RavuAlHemio/trainbuttons/code/on_board/stm32g0b0/src/adc/cr.rs

#[doc = "Register `CR` reader"]
pub type R = crate::R<CrSpec>;
#[doc = "Register `CR` writer"]
pub type W = crate::W<CrSpec>;
#[doc = "ADC enable command This bit is set by software to enable the ADC. The ADC is effectively ready to operate once the ADRDY flag has been set. It is cleared by hardware when the ADC is disabled, after the execution of the ADDIS command. Note: The software is allowed to set ADEN only when all bits of ADC_CR registers are 0 (ADCAL=0, ADSTP=0, ADSTART=0, ADDIS=0 and ADEN=0)\n\nValue on reset: 0"]
#[derive(Clone, Copy, Debug, PartialEq, Eq)]
pub enum Aden {
    #[doc = "0: ADC is disabled (OFF state)"]
    B0x0 = 0,
    #[doc = "1: Write 1 to enable the ADC."]
    B0x1 = 1,
}
impl From<Aden> for bool {
    #[inline(always)]
    fn from(variant: Aden) -> Self {
        variant as u8 != 0
    }
}
#[doc = "Field `ADEN` reader - ADC enable command This bit is set by software to enable the ADC. The ADC is effectively ready to operate once the ADRDY flag has been set. It is cleared by hardware when the ADC is disabled, after the execution of the ADDIS command. Note: The software is allowed to set ADEN only when all bits of ADC_CR registers are 0 (ADCAL=0, ADSTP=0, ADSTART=0, ADDIS=0 and ADEN=0)"]
pub type AdenR = crate::BitReader<Aden>;
impl AdenR {
    #[doc = "Get enumerated values variant"]
    #[inline(always)]
    pub const fn variant(&self) -> Aden {
        match self.bits {
            false => Aden::B0x0,
            true => Aden::B0x1,
        }
    }
    #[doc = "ADC is disabled (OFF state)"]
    #[inline(always)]
    pub fn is_b_0x0(&self) -> bool {
        *self == Aden::B0x0
    }
    #[doc = "Write 1 to enable the ADC."]
    #[inline(always)]
    pub fn is_b_0x1(&self) -> bool {
        *self == Aden::B0x1
    }
}
#[doc = "Field `ADEN` writer - ADC enable command This bit is set by software to enable the ADC. The ADC is effectively ready to operate once the ADRDY flag has been set. It is cleared by hardware when the ADC is disabled, after the execution of the ADDIS command. Note: The software is allowed to set ADEN only when all bits of ADC_CR registers are 0 (ADCAL=0, ADSTP=0, ADSTART=0, ADDIS=0 and ADEN=0)"]
pub type AdenW<'a, REG> = crate::BitWriter<'a, REG, Aden>;
impl<'a, REG> AdenW<'a, REG>
where
    REG: crate::Writable + crate::RegisterSpec,
{
    #[doc = "ADC is disabled (OFF state)"]
    #[inline(always)]
    pub fn b_0x0(self) -> &'a mut crate::W<REG> {
        self.variant(Aden::B0x0)
    }
    #[doc = "Write 1 to enable the ADC."]
    #[inline(always)]
    pub fn b_0x1(self) -> &'a mut crate::W<REG> {
        self.variant(Aden::B0x1)
    }
}
#[doc = "ADC disable command This bit is set by software to disable the ADC (ADDIS command) and put it into power-down state (OFF state). It is cleared by hardware once the ADC is effectively disabled (ADEN is also cleared by hardware at this time). Note: Setting ADDIS to '1' is only effective when ADEN=1 and ADSTART=0 (which ensures that no conversion is ongoing)\n\nValue on reset: 0"]
#[derive(Clone, Copy, Debug, PartialEq, Eq)]
pub enum Addis {
    #[doc = "0: No ADDIS command ongoing"]
    B0x0 = 0,
    #[doc = "1: Write 1 to disable the ADC. Read 1 means that an ADDIS command is in progress."]
    B0x1 = 1,
}
impl From<Addis> for bool {
    #[inline(always)]
    fn from(variant: Addis) -> Self {
        variant as u8 != 0
    }
}
#[doc = "Field `ADDIS` reader - ADC disable command This bit is set by software to disable the ADC (ADDIS command) and put it into power-down state (OFF state). It is cleared by hardware once the ADC is effectively disabled (ADEN is also cleared by hardware at this time). Note: Setting ADDIS to '1' is only effective when ADEN=1 and ADSTART=0 (which ensures that no conversion is ongoing)"]
pub type AddisR = crate::BitReader<Addis>;
impl AddisR {
    #[doc = "Get enumerated values variant"]
    #[inline(always)]
    pub const fn variant(&self) -> Addis {
        match self.bits {
            false => Addis::B0x0,
            true => Addis::B0x1,
        }
    }
    #[doc = "No ADDIS command ongoing"]
    #[inline(always)]
    pub fn is_b_0x0(&self) -> bool {
        *self == Addis::B0x0
    }
    #[doc = "Write 1 to disable the ADC. Read 1 means that an ADDIS command is in progress."]
    #[inline(always)]
    pub fn is_b_0x1(&self) -> bool {
        *self == Addis::B0x1
    }
}
#[doc = "Field `ADDIS` writer - ADC disable command This bit is set by software to disable the ADC (ADDIS command) and put it into power-down state (OFF state). It is cleared by hardware once the ADC is effectively disabled (ADEN is also cleared by hardware at this time). Note: Setting ADDIS to '1' is only effective when ADEN=1 and ADSTART=0 (which ensures that no conversion is ongoing)"]
pub type AddisW<'a, REG> = crate::BitWriter<'a, REG, Addis>;
impl<'a, REG> AddisW<'a, REG>
where
    REG: crate::Writable + crate::RegisterSpec,
{
    #[doc = "No ADDIS command ongoing"]
    #[inline(always)]
    pub fn b_0x0(self) -> &'a mut crate::W<REG> {
        self.variant(Addis::B0x0)
    }
    #[doc = "Write 1 to disable the ADC. Read 1 means that an ADDIS command is in progress."]
    #[inline(always)]
    pub fn b_0x1(self) -> &'a mut crate::W<REG> {
        self.variant(Addis::B0x1)
    }
}
#[doc = "ADC start conversion command This bit is set by software to start ADC conversion. Depending on the EXTEN \\[1:0\\]
configuration bits, a conversion either starts immediately (software trigger configuration) or once a hardware trigger event occurs (hardware trigger configuration). It is cleared by hardware: In single conversion mode (CONT=0, DISCEN=0), when software trigger is selected (EXTEN=00): at the assertion of the end of Conversion Sequence (EOS) flag. In discontinuous conversion mode(CONT=0, DISCEN=1), when the software trigger is selected (EXTEN=00): at the assertion of the end of Conversion (EOC) flag. In all other cases: after the execution of the ADSTP command, at the same time as the ADSTP bit is cleared by hardware. Note: The software is allowed to set ADSTART only when ADEN=1 and ADDIS=0 (ADC is enabled and there is no pending request to disable the ADC). After writing to ADC_CHSELR register or changing CHSELRMOD or SCANDIRW, it is mandatory to wait until CCRDY flag is asserted before setting ADSTART, otherwise, the value written to ADSTART is ignored.\n\nValue on reset: 0"]
#[derive(Clone, Copy, Debug, PartialEq, Eq)]
pub enum Adstart {
    #[doc = "0: No ADC conversion is ongoing."]
    B0x0 = 0,
    #[doc = "1: Write 1 to start the ADC. Read 1 means that the ADC is operating and may be converting."]
    B0x1 = 1,
}
impl From<Adstart> for bool {
    #[inline(always)]
    fn from(variant: Adstart) -> Self {
        variant as u8 != 0
    }
}
#[doc = "Field `ADSTART` reader - ADC start conversion command This bit is set by software to start ADC conversion. Depending on the EXTEN \\[1:0\\]
configuration bits, a conversion either starts immediately (software trigger configuration) or once a hardware trigger event occurs (hardware trigger configuration). It is cleared by hardware: In single conversion mode (CONT=0, DISCEN=0), when software trigger is selected (EXTEN=00): at the assertion of the end of Conversion Sequence (EOS) flag. In discontinuous conversion mode(CONT=0, DISCEN=1), when the software trigger is selected (EXTEN=00): at the assertion of the end of Conversion (EOC) flag. In all other cases: after the execution of the ADSTP command, at the same time as the ADSTP bit is cleared by hardware. Note: The software is allowed to set ADSTART only when ADEN=1 and ADDIS=0 (ADC is enabled and there is no pending request to disable the ADC). After writing to ADC_CHSELR register or changing CHSELRMOD or SCANDIRW, it is mandatory to wait until CCRDY flag is asserted before setting ADSTART, otherwise, the value written to ADSTART is ignored."]
pub type AdstartR = crate::BitReader<Adstart>;
impl AdstartR {
    #[doc = "Get enumerated values variant"]
    #[inline(always)]
    pub const fn variant(&self) -> Adstart {
        match self.bits {
            false => Adstart::B0x0,
            true => Adstart::B0x1,
        }
    }
    #[doc = "No ADC conversion is ongoing."]
    #[inline(always)]
    pub fn is_b_0x0(&self) -> bool {
        *self == Adstart::B0x0
    }
    #[doc = "Write 1 to start the ADC. Read 1 means that the ADC is operating and may be converting."]
    #[inline(always)]
    pub fn is_b_0x1(&self) -> bool {
        *self == Adstart::B0x1
    }
}
#[doc = "Field `ADSTART` writer - ADC start conversion command This bit is set by software to start ADC conversion. Depending on the EXTEN \\[1:0\\]
configuration bits, a conversion either starts immediately (software trigger configuration) or once a hardware trigger event occurs (hardware trigger configuration). It is cleared by hardware: In single conversion mode (CONT=0, DISCEN=0), when software trigger is selected (EXTEN=00): at the assertion of the end of Conversion Sequence (EOS) flag. In discontinuous conversion mode(CONT=0, DISCEN=1), when the software trigger is selected (EXTEN=00): at the assertion of the end of Conversion (EOC) flag. In all other cases: after the execution of the ADSTP command, at the same time as the ADSTP bit is cleared by hardware. Note: The software is allowed to set ADSTART only when ADEN=1 and ADDIS=0 (ADC is enabled and there is no pending request to disable the ADC). After writing to ADC_CHSELR register or changing CHSELRMOD or SCANDIRW, it is mandatory to wait until CCRDY flag is asserted before setting ADSTART, otherwise, the value written to ADSTART is ignored."]
pub type AdstartW<'a, REG> = crate::BitWriter<'a, REG, Adstart>;
impl<'a, REG> AdstartW<'a, REG>
where
    REG: crate::Writable + crate::RegisterSpec,
{
    #[doc = "No ADC conversion is ongoing."]
    #[inline(always)]
    pub fn b_0x0(self) -> &'a mut crate::W<REG> {
        self.variant(Adstart::B0x0)
    }
    #[doc = "Write 1 to start the ADC. Read 1 means that the ADC is operating and may be converting."]
    #[inline(always)]
    pub fn b_0x1(self) -> &'a mut crate::W<REG> {
        self.variant(Adstart::B0x1)
    }
}
#[doc = "ADC stop conversion command This bit is set by software to stop and discard an ongoing conversion (ADSTP Command). It is cleared by hardware when the conversion is effectively discarded and the ADC is ready to accept a new start conversion command. Note: Setting ADSTP to '1' is only effective when ADSTART=1 and ADDIS=0 (ADC is enabled and may be converting and there is no pending request to disable the ADC)\n\nValue on reset: 0"]
#[derive(Clone, Copy, Debug, PartialEq, Eq)]
pub enum Adstp {
    #[doc = "0: No ADC stop conversion command ongoing"]
    B0x0 = 0,
    #[doc = "1: Write 1 to stop the ADC. Read 1 means that an ADSTP command is in progress."]
    B0x1 = 1,
}
impl From<Adstp> for bool {
    #[inline(always)]
    fn from(variant: Adstp) -> Self {
        variant as u8 != 0
    }
}
#[doc = "Field `ADSTP` reader - ADC stop conversion command This bit is set by software to stop and discard an ongoing conversion (ADSTP Command). It is cleared by hardware when the conversion is effectively discarded and the ADC is ready to accept a new start conversion command. Note: Setting ADSTP to '1' is only effective when ADSTART=1 and ADDIS=0 (ADC is enabled and may be converting and there is no pending request to disable the ADC)"]
pub type AdstpR = crate::BitReader<Adstp>;
impl AdstpR {
    #[doc = "Get enumerated values variant"]
    #[inline(always)]
    pub const fn variant(&self) -> Adstp {
        match self.bits {
            false => Adstp::B0x0,
            true => Adstp::B0x1,
        }
    }
    #[doc = "No ADC stop conversion command ongoing"]
    #[inline(always)]
    pub fn is_b_0x0(&self) -> bool {
        *self == Adstp::B0x0
    }
    #[doc = "Write 1 to stop the ADC. Read 1 means that an ADSTP command is in progress."]
    #[inline(always)]
    pub fn is_b_0x1(&self) -> bool {
        *self == Adstp::B0x1
    }
}
#[doc = "Field `ADSTP` writer - ADC stop conversion command This bit is set by software to stop and discard an ongoing conversion (ADSTP Command). It is cleared by hardware when the conversion is effectively discarded and the ADC is ready to accept a new start conversion command. Note: Setting ADSTP to '1' is only effective when ADSTART=1 and ADDIS=0 (ADC is enabled and may be converting and there is no pending request to disable the ADC)"]
pub type AdstpW<'a, REG> = crate::BitWriter<'a, REG, Adstp>;
impl<'a, REG> AdstpW<'a, REG>
where
    REG: crate::Writable + crate::RegisterSpec,
{
    #[doc = "No ADC stop conversion command ongoing"]
    #[inline(always)]
    pub fn b_0x0(self) -> &'a mut crate::W<REG> {
        self.variant(Adstp::B0x0)
    }
    #[doc = "Write 1 to stop the ADC. Read 1 means that an ADSTP command is in progress."]
    #[inline(always)]
    pub fn b_0x1(self) -> &'a mut crate::W<REG> {
        self.variant(Adstp::B0x1)
    }
}
#[doc = "ADC Voltage Regulator Enable This bit is set by software, to enable the ADC internal voltage regulator. The voltage regulator output is available after tADCVREG_SETUP. It is cleared by software to disable the voltage regulator. It can be cleared only if ADEN is et to 0. Note: The software is allowed to program this bit field only when the ADC is disabled (ADCAL=0, ADSTART=0, ADSTP=0, ADDIS=0 and ADEN=0).\n\nValue on reset: 0"]
#[derive(Clone, Copy, Debug, PartialEq, Eq)]
pub enum Advregen {
    #[doc = "0: ADC voltage regulator disabled"]
    B0x0 = 0,
    #[doc = "1: ADC voltage regulator enabled"]
    B0x1 = 1,
}
impl From<Advregen> for bool {
    #[inline(always)]
    fn from(variant: Advregen) -> Self {
        variant as u8 != 0
    }
}
#[doc = "Field `ADVREGEN` reader - ADC Voltage Regulator Enable This bit is set by software, to enable the ADC internal voltage regulator. The voltage regulator output is available after tADCVREG_SETUP. It is cleared by software to disable the voltage regulator. It can be cleared only if ADEN is et to 0. Note: The software is allowed to program this bit field only when the ADC is disabled (ADCAL=0, ADSTART=0, ADSTP=0, ADDIS=0 and ADEN=0)."]
pub type AdvregenR = crate::BitReader<Advregen>;
impl AdvregenR {
    #[doc = "Get enumerated values variant"]
    #[inline(always)]
    pub const fn variant(&self) -> Advregen {
        match self.bits {
            false => Advregen::B0x0,
            true => Advregen::B0x1,
        }
    }
    #[doc = "ADC voltage regulator disabled"]
    #[inline(always)]
    pub fn is_b_0x0(&self) -> bool {
        *self == Advregen::B0x0
    }
    #[doc = "ADC voltage regulator enabled"]
    #[inline(always)]
    pub fn is_b_0x1(&self) -> bool {
        *self == Advregen::B0x1
    }
}
#[doc = "Field `ADVREGEN` writer - ADC Voltage Regulator Enable This bit is set by software, to enable the ADC internal voltage regulator. The voltage regulator output is available after tADCVREG_SETUP. It is cleared by software to disable the voltage regulator. It can be cleared only if ADEN is et to 0. Note: The software is allowed to program this bit field only when the ADC is disabled (ADCAL=0, ADSTART=0, ADSTP=0, ADDIS=0 and ADEN=0)."]
pub type AdvregenW<'a, REG> = crate::BitWriter<'a, REG, Advregen>;
impl<'a, REG> AdvregenW<'a, REG>
where
    REG: crate::Writable + crate::RegisterSpec,
{
    #[doc = "ADC voltage regulator disabled"]
    #[inline(always)]
    pub fn b_0x0(self) -> &'a mut crate::W<REG> {
        self.variant(Advregen::B0x0)
    }
    #[doc = "ADC voltage regulator enabled"]
    #[inline(always)]
    pub fn b_0x1(self) -> &'a mut crate::W<REG> {
        self.variant(Advregen::B0x1)
    }
}
#[doc = "ADC calibration This bit is set by software to start the calibration of the ADC. It is cleared by hardware after calibration is complete. Note: The software is allowed to set ADCAL only when the ADC is disabled (ADCAL=0, ADSTART=0, ADSTP=0, ADDIS=0 and ADEN=0). The software is allowed to update the calibration factor by writing ADC_CALFACT only when ADEN=1 and ADSTART=0 (ADC enabled and no conversion is ongoing).\n\nValue on reset: 0"]
#[derive(Clone, Copy, Debug, PartialEq, Eq)]
pub enum Adcal {
    #[doc = "0: Calibration complete"]
    B0x0 = 0,
    #[doc = "1: Write 1 to calibrate the ADC. Read at 1 means that a calibration is in progress."]
    B0x1 = 1,
}
impl From<Adcal> for bool {
    #[inline(always)]
    fn from(variant: Adcal) -> Self {
        variant as u8 != 0
    }
}
#[doc = "Field `ADCAL` reader - ADC calibration This bit is set by software to start the calibration of the ADC. It is cleared by hardware after calibration is complete. Note: The software is allowed to set ADCAL only when the ADC is disabled (ADCAL=0, ADSTART=0, ADSTP=0, ADDIS=0 and ADEN=0). The software is allowed to update the calibration factor by writing ADC_CALFACT only when ADEN=1 and ADSTART=0 (ADC enabled and no conversion is ongoing)."]
pub type AdcalR = crate::BitReader<Adcal>;
impl AdcalR {
    #[doc = "Get enumerated values variant"]
    #[inline(always)]
    pub const fn variant(&self) -> Adcal {
        match self.bits {
            false => Adcal::B0x0,
            true => Adcal::B0x1,
        }
    }
    #[doc = "Calibration complete"]
    #[inline(always)]
    pub fn is_b_0x0(&self) -> bool {
        *self == Adcal::B0x0
    }
    #[doc = "Write 1 to calibrate the ADC. Read at 1 means that a calibration is in progress."]
    #[inline(always)]
    pub fn is_b_0x1(&self) -> bool {
        *self == Adcal::B0x1
    }
}
#[doc = "Field `ADCAL` writer - ADC calibration This bit is set by software to start the calibration of the ADC. It is cleared by hardware after calibration is complete. Note: The software is allowed to set ADCAL only when the ADC is disabled (ADCAL=0, ADSTART=0, ADSTP=0, ADDIS=0 and ADEN=0). The software is allowed to update the calibration factor by writing ADC_CALFACT only when ADEN=1 and ADSTART=0 (ADC enabled and no conversion is ongoing)."]
pub type AdcalW<'a, REG> = crate::BitWriter<'a, REG, Adcal>;
impl<'a, REG> AdcalW<'a, REG>
where
    REG: crate::Writable + crate::RegisterSpec,
{
    #[doc = "Calibration complete"]
    #[inline(always)]
    pub fn b_0x0(self) -> &'a mut crate::W<REG> {
        self.variant(Adcal::B0x0)
    }
    #[doc = "Write 1 to calibrate the ADC. Read at 1 means that a calibration is in progress."]
    #[inline(always)]
    pub fn b_0x1(self) -> &'a mut crate::W<REG> {
        self.variant(Adcal::B0x1)
    }
}
impl R {
    #[doc = "Bit 0 - ADC enable command This bit is set by software to enable the ADC. The ADC is effectively ready to operate once the ADRDY flag has been set. It is cleared by hardware when the ADC is disabled, after the execution of the ADDIS command. Note: The software is allowed to set ADEN only when all bits of ADC_CR registers are 0 (ADCAL=0, ADSTP=0, ADSTART=0, ADDIS=0 and ADEN=0)"]
    #[inline(always)]
    pub fn aden(&self) -> AdenR {
        AdenR::new((self.bits & 1) != 0)
    }
    #[doc = "Bit 1 - ADC disable command This bit is set by software to disable the ADC (ADDIS command) and put it into power-down state (OFF state). It is cleared by hardware once the ADC is effectively disabled (ADEN is also cleared by hardware at this time). Note: Setting ADDIS to '1' is only effective when ADEN=1 and ADSTART=0 (which ensures that no conversion is ongoing)"]
    #[inline(always)]
    pub fn addis(&self) -> AddisR {
        AddisR::new(((self.bits >> 1) & 1) != 0)
    }
    #[doc = "Bit 2 - ADC start conversion command This bit is set by software to start ADC conversion. Depending on the EXTEN \\[1:0\\]
configuration bits, a conversion either starts immediately (software trigger configuration) or once a hardware trigger event occurs (hardware trigger configuration). It is cleared by hardware: In single conversion mode (CONT=0, DISCEN=0), when software trigger is selected (EXTEN=00): at the assertion of the end of Conversion Sequence (EOS) flag. In discontinuous conversion mode(CONT=0, DISCEN=1), when the software trigger is selected (EXTEN=00): at the assertion of the end of Conversion (EOC) flag. In all other cases: after the execution of the ADSTP command, at the same time as the ADSTP bit is cleared by hardware. Note: The software is allowed to set ADSTART only when ADEN=1 and ADDIS=0 (ADC is enabled and there is no pending request to disable the ADC). After writing to ADC_CHSELR register or changing CHSELRMOD or SCANDIRW, it is mandatory to wait until CCRDY flag is asserted before setting ADSTART, otherwise, the value written to ADSTART is ignored."]
    #[inline(always)]
    pub fn adstart(&self) -> AdstartR {
        AdstartR::new(((self.bits >> 2) & 1) != 0)
    }
    #[doc = "Bit 4 - ADC stop conversion command This bit is set by software to stop and discard an ongoing conversion (ADSTP Command). It is cleared by hardware when the conversion is effectively discarded and the ADC is ready to accept a new start conversion command. Note: Setting ADSTP to '1' is only effective when ADSTART=1 and ADDIS=0 (ADC is enabled and may be converting and there is no pending request to disable the ADC)"]
    #[inline(always)]
    pub fn adstp(&self) -> AdstpR {
        AdstpR::new(((self.bits >> 4) & 1) != 0)
    }
    #[doc = "Bit 28 - ADC Voltage Regulator Enable This bit is set by software, to enable the ADC internal voltage regulator. The voltage regulator output is available after tADCVREG_SETUP. It is cleared by software to disable the voltage regulator. It can be cleared only if ADEN is et to 0. Note: The software is allowed to program this bit field only when the ADC is disabled (ADCAL=0, ADSTART=0, ADSTP=0, ADDIS=0 and ADEN=0)."]
    #[inline(always)]
    pub fn advregen(&self) -> AdvregenR {
        AdvregenR::new(((self.bits >> 28) & 1) != 0)
    }
    #[doc = "Bit 31 - ADC calibration This bit is set by software to start the calibration of the ADC. It is cleared by hardware after calibration is complete. Note: The software is allowed to set ADCAL only when the ADC is disabled (ADCAL=0, ADSTART=0, ADSTP=0, ADDIS=0 and ADEN=0). The software is allowed to update the calibration factor by writing ADC_CALFACT only when ADEN=1 and ADSTART=0 (ADC enabled and no conversion is ongoing)."]
    #[inline(always)]
    pub fn adcal(&self) -> AdcalR {
        AdcalR::new(((self.bits >> 31) & 1) != 0)
    }
}
impl W {
    #[doc = "Bit 0 - ADC enable command This bit is set by software to enable the ADC. The ADC is effectively ready to operate once the ADRDY flag has been set. It is cleared by hardware when the ADC is disabled, after the execution of the ADDIS command. Note: The software is allowed to set ADEN only when all bits of ADC_CR registers are 0 (ADCAL=0, ADSTP=0, ADSTART=0, ADDIS=0 and ADEN=0)"]
    #[inline(always)]
    #[must_use]
    pub fn aden(&mut self) -> AdenW<CrSpec> {
        AdenW::new(self, 0)
    }
    #[doc = "Bit 1 - ADC disable command This bit is set by software to disable the ADC (ADDIS command) and put it into power-down state (OFF state). It is cleared by hardware once the ADC is effectively disabled (ADEN is also cleared by hardware at this time). Note: Setting ADDIS to '1' is only effective when ADEN=1 and ADSTART=0 (which ensures that no conversion is ongoing)"]
    #[inline(always)]
    #[must_use]
    pub fn addis(&mut self) -> AddisW<CrSpec> {
        AddisW::new(self, 1)
    }
    #[doc = "Bit 2 - ADC start conversion command This bit is set by software to start ADC conversion. Depending on the EXTEN \\[1:0\\]
configuration bits, a conversion either starts immediately (software trigger configuration) or once a hardware trigger event occurs (hardware trigger configuration). It is cleared by hardware: In single conversion mode (CONT=0, DISCEN=0), when software trigger is selected (EXTEN=00): at the assertion of the end of Conversion Sequence (EOS) flag. In discontinuous conversion mode(CONT=0, DISCEN=1), when the software trigger is selected (EXTEN=00): at the assertion of the end of Conversion (EOC) flag. In all other cases: after the execution of the ADSTP command, at the same time as the ADSTP bit is cleared by hardware. Note: The software is allowed to set ADSTART only when ADEN=1 and ADDIS=0 (ADC is enabled and there is no pending request to disable the ADC). After writing to ADC_CHSELR register or changing CHSELRMOD or SCANDIRW, it is mandatory to wait until CCRDY flag is asserted before setting ADSTART, otherwise, the value written to ADSTART is ignored."]
    #[inline(always)]
    #[must_use]
    pub fn adstart(&mut self) -> AdstartW<CrSpec> {
        AdstartW::new(self, 2)
    }
    #[doc = "Bit 4 - ADC stop conversion command This bit is set by software to stop and discard an ongoing conversion (ADSTP Command). It is cleared by hardware when the conversion is effectively discarded and the ADC is ready to accept a new start conversion command. Note: Setting ADSTP to '1' is only effective when ADSTART=1 and ADDIS=0 (ADC is enabled and may be converting and there is no pending request to disable the ADC)"]
    #[inline(always)]
    #[must_use]
    pub fn adstp(&mut self) -> AdstpW<CrSpec> {
        AdstpW::new(self, 4)
    }
    #[doc = "Bit 28 - ADC Voltage Regulator Enable This bit is set by software, to enable the ADC internal voltage regulator. The voltage regulator output is available after tADCVREG_SETUP. It is cleared by software to disable the voltage regulator. It can be cleared only if ADEN is et to 0. Note: The software is allowed to program this bit field only when the ADC is disabled (ADCAL=0, ADSTART=0, ADSTP=0, ADDIS=0 and ADEN=0)."]
    #[inline(always)]
    #[must_use]
    pub fn advregen(&mut self) -> AdvregenW<CrSpec> {
        AdvregenW::new(self, 28)
    }
    #[doc = "Bit 31 - ADC calibration This bit is set by software to start the calibration of the ADC. It is cleared by hardware after calibration is complete. Note: The software is allowed to set ADCAL only when the ADC is disabled (ADCAL=0, ADSTART=0, ADSTP=0, ADDIS=0 and ADEN=0). The software is allowed to update the calibration factor by writing ADC_CALFACT only when ADEN=1 and ADSTART=0 (ADC enabled and no conversion is ongoing)."]
    #[inline(always)]
    #[must_use]
    pub fn adcal(&mut self) -> AdcalW<CrSpec> {
        AdcalW::new(self, 31)
    }
}
#[doc = "ADC control register\n\nYou can [`read`](crate::Reg::read) this register and get [`cr::R`](R). You can [`reset`](crate::Reg::reset), [`write`](crate::Reg::write), [`write_with_zero`](crate::Reg::write_with_zero) this register using [`cr::W`](W). You can also [`modify`](crate::Reg::modify) this register. See [API](https://docs.rs/svd2rust/#read--modify--write-api)."]
pub struct CrSpec;
impl crate::RegisterSpec for CrSpec {
    type Ux = u32;
}
#[doc = "`read()` method returns [`cr::R`](R) reader structure"]
impl crate::Readable for CrSpec {}
#[doc = "`write(|w| ..)` method takes [`cr::W`](W) writer structure"]
impl crate::Writable for CrSpec {
    type Safety = crate::Unsafe;
    const ZERO_TO_MODIFY_FIELDS_BITMAP: u32 = 0;
    const ONE_TO_MODIFY_FIELDS_BITMAP: u32 = 0;
}
#[doc = "`reset()` method sets CR to value 0"]
impl crate::Resettable for CrSpec {
    const RESET_VALUE: u32 = 0;
}
