RavuAlHemio/trainbuttons/code/on_board/stm32g0b0/src/adc/isr.rs

#[doc = "Register `ISR` reader"]
pub type R = crate::R<IsrSpec>;
#[doc = "Register `ISR` writer"]
pub type W = crate::W<IsrSpec>;
#[doc = "ADC ready This bit is set by hardware after the ADC has been enabled (ADEN=1) and when the ADC reaches a state where it is ready to accept conversion requests. It is cleared by software writing 1 to it.\n\nValue on reset: 0"]
#[derive(Clone, Copy, Debug, PartialEq, Eq)]
pub enum Adrdy {
    #[doc = "0: ADC not yet ready to start conversion (or the flag event was already acknowledged and cleared by software)"]
    B0x0 = 0,
    #[doc = "1: ADC is ready to start conversion"]
    B0x1 = 1,
}
impl From<Adrdy> for bool {
    #[inline(always)]
    fn from(variant: Adrdy) -> Self {
        variant as u8 != 0
    }
}
#[doc = "Field `ADRDY` reader - ADC ready This bit is set by hardware after the ADC has been enabled (ADEN=1) and when the ADC reaches a state where it is ready to accept conversion requests. It is cleared by software writing 1 to it."]
pub type AdrdyR = crate::BitReader<Adrdy>;
impl AdrdyR {
    #[doc = "Get enumerated values variant"]
    #[inline(always)]
    pub const fn variant(&self) -> Adrdy {
        match self.bits {
            false => Adrdy::B0x0,
            true => Adrdy::B0x1,
        }
    }
    #[doc = "ADC not yet ready to start conversion (or the flag event was already acknowledged and cleared by software)"]
    #[inline(always)]
    pub fn is_b_0x0(&self) -> bool {
        *self == Adrdy::B0x0
    }
    #[doc = "ADC is ready to start conversion"]
    #[inline(always)]
    pub fn is_b_0x1(&self) -> bool {
        *self == Adrdy::B0x1
    }
}
#[doc = "Field `ADRDY` writer - ADC ready This bit is set by hardware after the ADC has been enabled (ADEN=1) and when the ADC reaches a state where it is ready to accept conversion requests. It is cleared by software writing 1 to it."]
pub type AdrdyW<'a, REG> = crate::BitWriter<'a, REG, Adrdy>;
impl<'a, REG> AdrdyW<'a, REG>
where
    REG: crate::Writable + crate::RegisterSpec,
{
    #[doc = "ADC not yet ready to start conversion (or the flag event was already acknowledged and cleared by software)"]
    #[inline(always)]
    pub fn b_0x0(self) -> &'a mut crate::W<REG> {
        self.variant(Adrdy::B0x0)
    }
    #[doc = "ADC is ready to start conversion"]
    #[inline(always)]
    pub fn b_0x1(self) -> &'a mut crate::W<REG> {
        self.variant(Adrdy::B0x1)
    }
}
#[doc = "End of sampling flag This bit is set by hardware during the conversion, at the end of the sampling phase.It is cleared by software by programming it to '1'.\n\nValue on reset: 0"]
#[derive(Clone, Copy, Debug, PartialEq, Eq)]
pub enum Eosmp {
    #[doc = "0: Not at the end of the sampling phase (or the flag event was already acknowledged and cleared by software)"]
    B0x0 = 0,
    #[doc = "1: End of sampling phase reached"]
    B0x1 = 1,
}
impl From<Eosmp> for bool {
    #[inline(always)]
    fn from(variant: Eosmp) -> Self {
        variant as u8 != 0
    }
}
#[doc = "Field `EOSMP` reader - End of sampling flag This bit is set by hardware during the conversion, at the end of the sampling phase.It is cleared by software by programming it to '1'."]
pub type EosmpR = crate::BitReader<Eosmp>;
impl EosmpR {
    #[doc = "Get enumerated values variant"]
    #[inline(always)]
    pub const fn variant(&self) -> Eosmp {
        match self.bits {
            false => Eosmp::B0x0,
            true => Eosmp::B0x1,
        }
    }
    #[doc = "Not at the end of the sampling phase (or the flag event was already acknowledged and cleared by software)"]
    #[inline(always)]
    pub fn is_b_0x0(&self) -> bool {
        *self == Eosmp::B0x0
    }
    #[doc = "End of sampling phase reached"]
    #[inline(always)]
    pub fn is_b_0x1(&self) -> bool {
        *self == Eosmp::B0x1
    }
}
#[doc = "Field `EOSMP` writer - End of sampling flag This bit is set by hardware during the conversion, at the end of the sampling phase.It is cleared by software by programming it to '1'."]
pub type EosmpW<'a, REG> = crate::BitWriter<'a, REG, Eosmp>;
impl<'a, REG> EosmpW<'a, REG>
where
    REG: crate::Writable + crate::RegisterSpec,
{
    #[doc = "Not at the end of the sampling phase (or the flag event was already acknowledged and cleared by software)"]
    #[inline(always)]
    pub fn b_0x0(self) -> &'a mut crate::W<REG> {
        self.variant(Eosmp::B0x0)
    }
    #[doc = "End of sampling phase reached"]
    #[inline(always)]
    pub fn b_0x1(self) -> &'a mut crate::W<REG> {
        self.variant(Eosmp::B0x1)
    }
}
#[doc = "End of conversion flag This bit is set by hardware at the end of each conversion of a channel when a new data result is available in the ADC_DR register. It is cleared by software writing 1 to it or by reading the ADC_DR register.\n\nValue on reset: 0"]
#[derive(Clone, Copy, Debug, PartialEq, Eq)]
pub enum Eoc {
    #[doc = "0: Channel conversion not complete (or the flag event was already acknowledged and cleared by software)"]
    B0x0 = 0,
    #[doc = "1: Channel conversion complete"]
    B0x1 = 1,
}
impl From<Eoc> for bool {
    #[inline(always)]
    fn from(variant: Eoc) -> Self {
        variant as u8 != 0
    }
}
#[doc = "Field `EOC` reader - End of conversion flag This bit is set by hardware at the end of each conversion of a channel when a new data result is available in the ADC_DR register. It is cleared by software writing 1 to it or by reading the ADC_DR register."]
pub type EocR = crate::BitReader<Eoc>;
impl EocR {
    #[doc = "Get enumerated values variant"]
    #[inline(always)]
    pub const fn variant(&self) -> Eoc {
        match self.bits {
            false => Eoc::B0x0,
            true => Eoc::B0x1,
        }
    }
    #[doc = "Channel conversion not complete (or the flag event was already acknowledged and cleared by software)"]
    #[inline(always)]
    pub fn is_b_0x0(&self) -> bool {
        *self == Eoc::B0x0
    }
    #[doc = "Channel conversion complete"]
    #[inline(always)]
    pub fn is_b_0x1(&self) -> bool {
        *self == Eoc::B0x1
    }
}
#[doc = "Field `EOC` writer - End of conversion flag This bit is set by hardware at the end of each conversion of a channel when a new data result is available in the ADC_DR register. It is cleared by software writing 1 to it or by reading the ADC_DR register."]
pub type EocW<'a, REG> = crate::BitWriter<'a, REG, Eoc>;
impl<'a, REG> EocW<'a, REG>
where
    REG: crate::Writable + crate::RegisterSpec,
{
    #[doc = "Channel conversion not complete (or the flag event was already acknowledged and cleared by software)"]
    #[inline(always)]
    pub fn b_0x0(self) -> &'a mut crate::W<REG> {
        self.variant(Eoc::B0x0)
    }
    #[doc = "Channel conversion complete"]
    #[inline(always)]
    pub fn b_0x1(self) -> &'a mut crate::W<REG> {
        self.variant(Eoc::B0x1)
    }
}
#[doc = "End of sequence flag This bit is set by hardware at the end of the conversion of a sequence of channels selected by the CHSEL bits. It is cleared by software writing 1 to it.\n\nValue on reset: 0"]
#[derive(Clone, Copy, Debug, PartialEq, Eq)]
pub enum Eos {
    #[doc = "0: Conversion sequence not complete (or the flag event was already acknowledged and cleared by software)"]
    B0x0 = 0,
    #[doc = "1: Conversion sequence complete"]
    B0x1 = 1,
}
impl From<Eos> for bool {
    #[inline(always)]
    fn from(variant: Eos) -> Self {
        variant as u8 != 0
    }
}
#[doc = "Field `EOS` reader - End of sequence flag This bit is set by hardware at the end of the conversion of a sequence of channels selected by the CHSEL bits. It is cleared by software writing 1 to it."]
pub type EosR = crate::BitReader<Eos>;
impl EosR {
    #[doc = "Get enumerated values variant"]
    #[inline(always)]
    pub const fn variant(&self) -> Eos {
        match self.bits {
            false => Eos::B0x0,
            true => Eos::B0x1,
        }
    }
    #[doc = "Conversion sequence not complete (or the flag event was already acknowledged and cleared by software)"]
    #[inline(always)]
    pub fn is_b_0x0(&self) -> bool {
        *self == Eos::B0x0
    }
    #[doc = "Conversion sequence complete"]
    #[inline(always)]
    pub fn is_b_0x1(&self) -> bool {
        *self == Eos::B0x1
    }
}
#[doc = "Field `EOS` writer - End of sequence flag This bit is set by hardware at the end of the conversion of a sequence of channels selected by the CHSEL bits. It is cleared by software writing 1 to it."]
pub type EosW<'a, REG> = crate::BitWriter<'a, REG, Eos>;
impl<'a, REG> EosW<'a, REG>
where
    REG: crate::Writable + crate::RegisterSpec,
{
    #[doc = "Conversion sequence not complete (or the flag event was already acknowledged and cleared by software)"]
    #[inline(always)]
    pub fn b_0x0(self) -> &'a mut crate::W<REG> {
        self.variant(Eos::B0x0)
    }
    #[doc = "Conversion sequence complete"]
    #[inline(always)]
    pub fn b_0x1(self) -> &'a mut crate::W<REG> {
        self.variant(Eos::B0x1)
    }
}
#[doc = "ADC overrun This bit is set by hardware when an overrun occurs, meaning that a new conversion has complete while the EOC flag was already set. It is cleared by software writing 1 to it.\n\nValue on reset: 0"]
#[derive(Clone, Copy, Debug, PartialEq, Eq)]
pub enum Ovr {
    #[doc = "0: No overrun occurred (or the flag event was already acknowledged and cleared by software)"]
    B0x0 = 0,
    #[doc = "1: Overrun has occurred"]
    B0x1 = 1,
}
impl From<Ovr> for bool {
    #[inline(always)]
    fn from(variant: Ovr) -> Self {
        variant as u8 != 0
    }
}
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
